jeffqchen/RetroTINK-5X-SCART-Dock/BNC_Dock/Pics/06.jpg

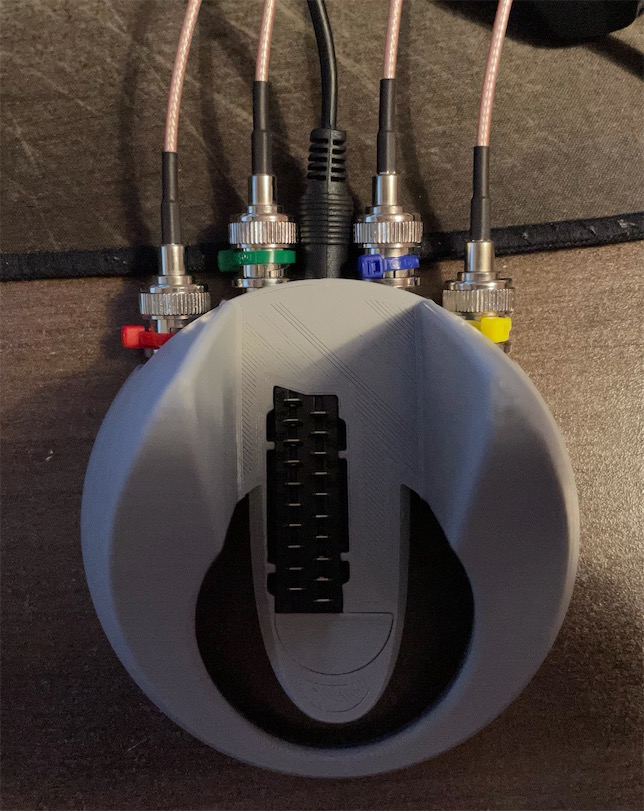
BNC_Dock/Pics/06.jpg
